MartinP1/ESP8266_MQTT_THERMOSTAT/unspecialized_mqtt_doings.h

#if 0
void DumpFreeRAM(){ 
  Serial.print(" free Heap: ");
  Serial.print(ESP.getFreeHeap());
  Serial.print("/");
  Serial.print(ESP.getHeapSize());
  Serial.print(" min free heap: ");
  Serial.print(ESP.getMinFreeHeap());
  Serial.print(" free PSRAM: ");
  Serial.print(ESP.getFreePsram());
  Serial.print(" ResetReason: ");
  Serial.print(rstReason[0]);
  Serial.print("/");
  Serial.println(rstReason[1]);

} 
#endif

void DumpSysInfo(){
  Serial.print("Firmware-Version: "); 
  Serial.print(VERSION_NO);
  Serial.print(" IP-Address: ");
  Serial.println(WiFi.localIP());
}  


void connectToWifi() {
  Serial.print("Client ");
  Serial.print(MQTT_PUB_DEV_PREFIX);
  Serial.print(" Connecting to Wi-Fi ");
  Serial.println(WIFI_SSID);
  WiFi.setScanMethod(WIFI_ALL_CHANNEL_SCAN);
  WiFi.setSortMethod(WIFI_CONNECT_AP_BY_SIGNAL);
  WiFi.begin(WIFI_SSID, WIFI_PASSWORD);
}


void connectToMqtt() {
  Serial.print("Connecting to MQTT Broker ");
  Serial.print(MQTT_HOST);
  Serial.print(":");
  Serial.println(MQTT_PORT);

  mqttClient.connect();
}


#if defined(ARDUINO_D1_MINI32) || defined(ARDUINO_LOLIN_S2_MINI)
// ARDUINO_EVENT_WIFI_STA_GOT_IP
// 
// ARDUINO_EVENT_WIFI_STA_DISCONNECTED
void onWifiConnect(WiFiEvent_t event, WiFiEventInfo_t info) {
  Serial.print("Connected to Wi-Fi - ");
  Serial.print(WIFI_SSID);
  Serial.print(" Signal strength:");
  Serial.println(WiFi.RSSI());
  // Serial.print(" ResetReason: ");
  // Serial.print(rstReason[0]);
  // Serial.print("/");
  // Serial.println(rstReason[1]);
  //DumpFreeRAM();
  connectToMqtt();
}

void onWifiDisconnect(WiFiEvent_t event, WiFiEventInfo_t info) {
  Serial.println("Disconnected from Wi-Fi.");
  // mqttReconnectTimer.detach(); // ensure we don't reconnect to MQTT while reconnecting to Wi-Fi
  // wifiReconnectTimer.once(2, connectToWifi);
  uiWifiDisconnects++;
}
#else
void onWifiConnect(const WiFiEventStationModeGotIP& event) {
  Serial.print("Connected to Wi-Fi - ");
  Serial.print(" Signal strength:");
  Serial.println(WiFi.RSSI());
  // connectToMqtt();
}

void onWifiDisconnect(const WiFiEventStationModeDisconnected& event) {
  Serial.println("Disconnected from Wi-Fi.");
  // mqttReconnectTimer.detach(); // ensure we don't reconnect to MQTT while reconnecting to Wi-Fi
  // wifiReconnectTimer.once(2, connectToWifi);
}
#endif
