MartinP1/ESP8266_MQTT_THERMOSTAT/MqttBindings.h

void DefaultCallback(const char* value) {
  Serial.println("BINDING-Default callback: ");
  // Serial.println(value);
}

void setMQTTBindings() {
   tempHystNode.SetBinding((MQTT_PUB_DES_PREFIX + MQTT_PUB_TEMPHYST_SUFFIX).c_str(),DefaultCallback);
}
