MartinP1/ESP8266_MQTT_THERMOSTAT/MqttLogging.h

  char log_buffer[120];


void MQTTLog(const char* logmsg){
    
    Serial.print("mqttlog "); 
    Serial.println(logmsg);
    if (mqttClient.connected()) {
      uint16_t packetIdPub1 = mqttClient.publish((MQTT_PUB_DEV_PREFIX + "/logmsg").c_str(), 1, true, logmsg); 
      delay(10);                   
    }        
}


void MQTTLogPrintf (const char* format, ...){
  va_list args;
  va_start (args, format);
  if (!mqttClient.connected())
    return;
  vsnprintf (log_buffer,119,format, args);
  uint16_t packetIdPub1 = mqttClient.publish((MQTT_PUB_DEV_PREFIX + "/logmsg").c_str(), 1, true, log_buffer);    
  delay(10);                        
  va_end (args);
}
